bkw777/WiModem_to_100/WiModem_to_100.sch

## KiCad design WiModem_to_100.sch (2020-08-16, an earlier design)

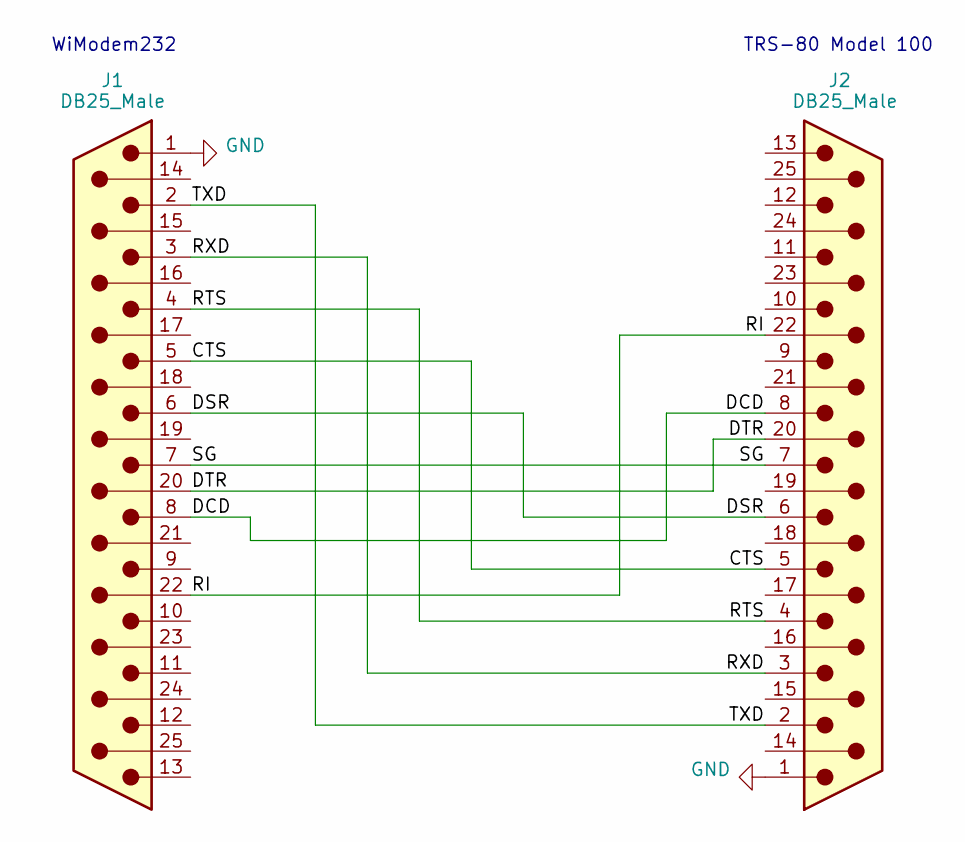
[picture p6: schematic WiModem_to_100.sch]

Parts:
J1: DB25_Male; DSUB-25_Male_EdgeMount_P2.77mm
J2: DB25_Male; DSUB-25_Male_Vertical_P2.77x2.84mm

Connections:
CTS: J1.5, J2.5
DCD: J1.8, J2.8
DSR: J1.6, J2.6
DTR: J1.20, J2.20
GND: J1.1, J2.1
RI: J1.22, J2.22
RTS: J1.4, J2.4
RXD: J1.3, J2.3
SG: J1.7, J2.7
TXD: J1.2, J2.2

Notes on the sheet:
WiModem232
TRS-80 Model 100
